t6z/christmas-tree/src/notes.c

#include "notes.h"

uint16_t tca0_per[NUM_NOTES] = {
   0x638,0x5DF,
   0x58A,0x53B,
   0x4F0,0x4A9,
   0x466,0x426,
   0x3EB,0x3B2,
   0x37D,0x34B
};

uint16_t tca0_cmp0[NUM_NOTES] = {
   0x31C,0x2EF,
   0x2C5,0x29D,
   0x278,0x254,
   0x233,0x213,
   0x1F5,0x1D9,
   0x1BE,0x1A5
};
